snhobbs/parametric-test-jig/source/press-jig-type-a/objects/assembly.scad

use<press-jig-type-a/assembly.scad>;
/* [View] */
$fa=1;
$fs=1;
$fn=100;
$preview=true;
$vpr = [ 83.00, 0.00, 6.10 ];
$vpd=140.0;

assembly();
