snhobbs/parametric-test-jig/source/press-jig-type-a/objects/base-pcb-outline.scad

use<press-jig-type-a/assembly.scad>;
$fs=0.1;
base_pcb_outline();
