snhobbs/parametric-test-jig/source/press-jig-type-a/objects/base-plate-outline.scad

use<press-jig-type-a/assembly.scad>;
$fs=0.1;
base_plate_outline();
