snhobbs/parametric-test-jig/source/press-jig-type-a/objects/cradle-support-bracket-outline.scad

use<press-jig-type-a/assembly.scad>;
$fs=0.1;
cradle_support_bracket_outline();
