snhobbs/parametric-test-jig/source/press-jig-type-a/objects/cradle_assembly.scad

use<press-jig-type-a/cradle_assembly.scad>;
$fs=0.1;
cradle_assembly();
