snhobbs/parametric-test-jig/source/press-jig-type-a/objects/pressure-plate-outline.scad

use<press-jig-type-a/assembly.scad>;
$fs=0.1;
$fn=1000;
 pressure_plate_outline();
