snhobbs/parametric-test-jig/source/press-jig-type-a/objects/support-plate-jig-a-outline.scad

use<press-jig-type-a/assembly.scad>;
$fs=0.1;
support_plate_outline();
