snhobbs/parametric-test-jig/example/sensor/alignment-pins.scad

/* x, y, type */
function get_design_pins(pin_depth = -2) = [
    [24, 39, "GP-2S-44", pin_depth],
    [-24, 39, "GP-2S-44", pin_depth],
    [24, -39, "GP-2S-44", pin_depth],
    [-24, -39, "GP-2S-44", pin_depth],
    ];
