snhobbs/parametric-test-jig/example/sensor/pressure-pins.scad

/* x, y, [hole diameter, tip diameter, base diameter, taper length] */
function get_pressure_pins(pin_depth = -2) = [
    [18, -39.0, [3.2,6,8,2.5]],
    [-22, -33.0, [3.2,6,8,2.5]],
    [0, -19.5, [3.2,6,8,2.5]],
    [0, 15.0, [3.2,6,8,2.5]],
    [24, 34.0, [3.2,6,8,2.5]],
    [-16, 28.0, [3.2,6,8,2.5]],
    [-17, 0.0, [3.2,6,8,2.5]],
    [14, 0.0, [3.2,6,8,2.5]],
    ];
