snhobbs/parametric-test-jig/source/press-jig-type-a/objects/design-under-test-pcb-outline.scad

use<press-jig-type-a/assembly.scad>;
$fs=0.1;
dut_pcb_outline();
